MertX2/PowerStripHavoc/Firmware/firm/src/BQ2589x.cpp

/*                                                     https://oshwlab.com/ratti3
  _|_|_|                _|      _|      _|  _|_|_|     https://youtube.com/@Ratti3
  _|    _|    _|_|_|  _|_|_|_|_|_|_|_|            _|   https://projecthub.arduino.cc/Ratti3
  _|_|_|    _|    _|    _|      _|      _|    _|_|     https://ratti3.blogspot.com
  _|    _|  _|    _|    _|      _|      _|        _|   https://hackaday.io/Ratti3
  _|    _|    _|_|_|      _|_|    _|_|  _|  _|_|_|     https://www.hackster.io/Ratti3
                                                       https://github.com/Ratti3

Code forked from https://github.com/spencer1979/bq2589x

This file is part of https://github.com/Ratti3/BQ2589x-ATMEGA32U4-Charger-Powerbank-with-SSD1306-OLED

BQ2589x-ATMEGA32U4-Charger-Powerbank-with-SSD1306-OLED is free software: you can redistribute it and/or modify it under the terms of the
GNU General Public License as published by the Free Software Foundation, either version 3 of the License, or (at your option) any later version.
BQ2589x-ATMEGA32U4-Charger-Powerbank-with-SSD1306-OLED is distributed in the hope that it will be useful, but WITHOUT ANY WARRANTY;
without even the implied warranty of MERCHANTABILITY or FITNESS FOR A PARTICULAR PURPOSE. See the GNU General Public License for more details.
You should have received a copy of the GNU General Public License along with BQ2589x-ATMEGA32U4-Charger-Powerbank-with-SSD1306-OLED. If not, see <https://www.gnu.org/licenses/>.
*/

#include "BQ2589x.h"

int bq2589x::begin(TwoWire *theWire, uint8_t addr)
{
    _wire = theWire;
    _i2caddr = addr;
    return reset_chip();
}

int bq2589x::read_byte(uint8_t *data, uint8_t reg)
{

    int rtn;
    _wire->beginTransmission((uint8_t)_i2caddr);
    _wire->write(reg);
    rtn = _wire->endTransmission();

    _wire->requestFrom((uint8_t)_i2caddr, (uint8_t)1);
    delayMicroseconds(100);
    *data = _wire->read();

    if (rtn == I2C_OK)
    {
        return BQ2589X_OK; //TI lib uses 1 as failed
    }
    else
    {
        return BQ2589X_ERR; //TI lib uses 1 as failed
    }
}

int bq2589x::write_byte(uint8_t reg, uint8_t data)
{
    int rtn;
    _wire->beginTransmission((uint8_t)_i2caddr);
    _wire->write((uint8_t)reg);
    _wire->write((uint8_t)data);
    rtn = _wire->endTransmission();

    if (rtn == I2C_OK)
    {
        return BQ2589X_OK; //TI lib uses 1 as failed
    }
    else
    {
        return BQ2589X_ERR; //TI lib uses 1 as failed
    }
}

int bq2589x::update_bits(uint8_t reg, uint8_t mask, uint8_t data)
{
    int ret;
    uint8_t tmp;

    ret = read_byte(&tmp, reg);

    if (ret)
        return ret;

    tmp &= ~mask;
    tmp |= data & mask;

    return write_byte(reg, tmp);
}

int bq2589x::get_vbus_type()
{
    uint8_t val = 0;
    int ret;

    ret = read_byte(&val, BQ2589X_REG_0B);
    if (ret)
        return (BQ2589X_VBUS_UNKNOWN);
    val &= BQ2589X_VBUS_STAT_MASK;
    val >>= BQ2589X_VBUS_STAT_SHIFT;

    return val;
}

String bq2589x::get_vbus_type_text()
{
    switch (get_vbus_type()) {
    case 0:
        return BQ2589X_VBUS_STAT_00;
        break;
    case 1:
        return BQ2589X_VBUS_STAT_01;
        break;
    case 2:
        return BQ2589X_VBUS_STAT_02;
        break;
    case 3:
        return BQ2589X_VBUS_STAT_03;
        break;
    case 4:
        return BQ2589X_VBUS_STAT_04;
        break;
    case 5:
        return BQ2589X_VBUS_STAT_05;
        break;
    case 6:
        return BQ2589X_VBUS_STAT_06;
        break;
    case 7:
        return BQ2589X_VBUS_STAT_07;
        break;
    default:
        return BQ2589X_VBUS_STAT_XX;
        break;
    }
}

int bq2589x::enable_otg()
{
    uint8_t val = BQ2589X_OTG_ENABLE << BQ2589X_OTG_CONFIG_SHIFT;
    return update_bits(BQ2589X_REG_03, BQ2589X_OTG_CONFIG_MASK, val);
}

int bq2589x::disable_otg()
{
    uint8_t val = BQ2589X_OTG_DISABLE << BQ2589X_OTG_CONFIG_SHIFT;
    return update_bits(BQ2589X_REG_03, BQ2589X_OTG_CONFIG_MASK, val);
}

bool bq2589x::is_otg_enabled()
{
    uint8_t val;

    read_byte(&val, BQ2589X_REG_03);
    val &= BQ2589X_OTG_CONFIG_MASK;
    val >>= BQ2589X_OTG_CONFIG_SHIFT;

    return (bool)(val);
}

int bq2589x::set_otg_voltage(uint16_t volt)
{
    uint8_t val = 0;

    if (volt < BQ2589X_BOOSTV_BASE)
        volt = BQ2589X_BOOSTV_BASE;
    if (volt > BQ2589X_BOOSTV_BASE + (BQ2589X_BOOSTV_MASK >> BQ2589X_BOOSTV_SHIFT) * BQ2589X_BOOSTV_LSB)
        volt = BQ2589X_BOOSTV_BASE + (BQ2589X_BOOSTV_MASK >> BQ2589X_BOOSTV_SHIFT) * BQ2589X_BOOSTV_LSB;

    val = ((volt - BQ2589X_BOOSTV_BASE) / BQ2589X_BOOSTV_LSB) << BQ2589X_BOOSTV_SHIFT;
    return update_bits(BQ2589X_REG_0A, BQ2589X_BOOSTV_MASK, val);
}

int bq2589x::get_otg_voltage()
{
    uint8_t val;
    int volt;
    int ret;

    ret = read_byte(&val, BQ2589X_REG_0A);
    if (ret)
    {
        return ret;
    }
    else
    {
        volt = (BQ2589X_BOOSTV_BASE + ((val & BQ2589X_BOOSTV_MASK) >> BQ2589X_BOOSTV_SHIFT) * BQ2589X_BOOSTV_LSB);
        return volt;
    }
}

int bq2589x::set_otg_current(int curr)
{
    uint8_t temp;

    if (curr == 500)
        temp = BQ2589X_BOOST_LIM_500MA;
    else if (curr == 750)
        temp = BQ2589X_BOOST_LIM_750MA;
    else if (curr == 1200)
        temp = BQ2589X_BOOST_LIM_1200MA;
    else if (curr == 1400)
        temp = BQ2589X_BOOST_LIM_1400MA;
    else if (curr == 1650)
        temp = BQ2589X_BOOST_LIM_1650MA;
    else if (curr == 1875)
        temp = BQ2589X_BOOST_LIM_1875MA;
    else if (curr == 2150)
        temp = BQ2589X_BOOST_LIM_2150MA;
    else
        temp = BQ2589X_BOOST_LIM_1400MA;

    return update_bits(BQ2589X_REG_0A, BQ2589X_BOOST_LIM_MASK, temp << BQ2589X_BOOST_LIM_SHIFT);
}

int bq2589x::get_otg_current()
{
    uint8_t val;
    int curr;
    int ret;

    ret = read_byte(&val, BQ2589X_REG_0A);
    if (ret)
    {
        return ret;
    }
    else
    {
        curr = (val & BQ2589X_BOOST_LIM_MASK) >> BQ2589X_BOOST_LIM_SHIFT;
        if (curr == 0)
            ret = BQ2589X_BOOST_LIM_500MA_VALUE;
        else if (curr == 1)
            ret = BQ2589X_BOOST_LIM_750MA_VALUE;
        else if (curr == 2)
            ret = BQ2589X_BOOST_LIM_1200MA_VALUE;
        else if (curr == 3)
            ret = BQ2589X_BOOST_LIM_1400MA_VALUE;
        else if (curr == 4)
            ret = BQ2589X_BOOST_LIM_1650MA_VALUE;
        else if (curr == 5)
            ret = BQ2589X_BOOST_LIM_1875MA_VALUE;
        else if (curr == 6)
            ret = BQ2589X_BOOST_LIM_2150MA_VALUE;
    }
    return ret;
}

int bq2589x::enable_charger()
{
    uint8_t val = BQ2589X_CHG_ENABLE << BQ2589X_CHG_CONFIG_SHIFT;
    return update_bits(BQ2589X_REG_03, BQ2589X_CHG_CONFIG_MASK, val);
}

int bq2589x::disable_charger()
{
    uint8_t val = BQ2589X_CHG_DISABLE << BQ2589X_CHG_CONFIG_SHIFT;
    return update_bits(BQ2589X_REG_03, BQ2589X_CHG_CONFIG_MASK, val);
}

bool bq2589x::is_charge_enabled()
{
    uint8_t val;

    read_byte(&val, BQ2589X_REG_03);
    val &= BQ2589X_CHG_CONFIG_MASK;
    val >>= BQ2589X_CHG_CONFIG_SHIFT;

    return (bool)(val);
}

int bq2589x::enable_bat_loaden()
{
    uint8_t val = BQ2589X_BAT_LOADEN_ENABLE << BQ2589X_BAT_LOADEN_SHIFT;
    return update_bits(BQ2589X_REG_03, BQ2589X_BAT_LOADEN_MASK, val);
}

int bq2589x::disable_bat_loaden()
{
    uint8_t val = BQ2589X_BAT_LOADEN_DISABLE << BQ2589X_BAT_LOADEN_SHIFT;
    return update_bits(BQ2589X_REG_03, BQ2589X_BAT_LOADEN_MASK, val);
}

/* interfaces that can be called by other module */
int bq2589x::adc_start(bool oneshot)
{
    uint8_t val;
    int ret;

    ret = read_byte(&val, BQ2589X_REG_02);
    if (ret)
    {
        return ret;
    }

    if (((val & BQ2589X_CONV_RATE_MASK) >> BQ2589X_CONV_RATE_SHIFT) == BQ2589X_ADC_CONTINUE_ENABLE)
        return BQ2589X_OK; /*is doing continuous scan*/
    if (oneshot)
        ret = update_bits(BQ2589X_REG_02, BQ2589X_CONV_START_MASK, BQ2589X_CONV_START << BQ2589X_CONV_START_SHIFT);
    else
        ret = update_bits(BQ2589X_REG_02, BQ2589X_CONV_RATE_MASK, BQ2589X_ADC_CONTINUE_ENABLE << BQ2589X_CONV_RATE_SHIFT);
    return ret;
}

int bq2589x::adc_stop()
{
    return update_bits(BQ2589X_REG_02, BQ2589X_CONV_RATE_MASK, BQ2589X_ADC_CONTINUE_DISABLE << BQ2589X_CONV_RATE_SHIFT);
}

int bq2589x::adc_read_battery_volt()
{
    uint8_t val;
    int volt;
    int ret;
    ret = read_byte(&val, BQ2589X_REG_0E);

    if (ret)
    {
        return ret;
    }
    else
    {
        volt = (BQ2589X_BATV_BASE + ((val & BQ2589X_BATV_MASK) >> BQ2589X_BATV_SHIFT) * BQ2589X_BATV_LSB);
        return volt;
    }
}

int bq2589x::adc_read_sys_volt()
{
    uint8_t val;
    int volt;
    int ret;
    ret = read_byte(&val, BQ2589X_REG_0F);

    if (ret)
    {
        return ret;
    }
    else
    {
        volt = BQ2589X_SYSV_BASE + ((val & BQ2589X_SYSV_MASK) >> BQ2589X_SYSV_SHIFT) * BQ2589X_SYSV_LSB;
        return volt;
    }
}

int bq2589x::adc_read_vbus_volt()
{
    uint8_t val;
    int volt;
    int ret;
    ret = read_byte(&val, BQ2589X_REG_11);

    if (ret)
    {
        return ret;
    }
    else
    {
        volt = BQ2589X_VBUSV_BASE + ((val & BQ2589X_VBUSV_MASK) >> BQ2589X_VBUSV_SHIFT) * BQ2589X_VBUSV_LSB;
        return volt;
    }
}

int bq2589x::adc_read_temperature()
{
    uint8_t val;
    int temp;
    int ret;
    ret = read_byte(&val, BQ2589X_REG_10);

    if (ret)
    {
        return ret;
    }
    else
    {
        temp = BQ2589X_TSPCT_BASE + ((val & BQ2589X_TSPCT_MASK) >> BQ2589X_TSPCT_SHIFT) * BQ2589X_TSPCT_LSB;
        return temp;
    }
}

int bq2589x::adc_read_charge_current()
{
    uint8_t val;
    int volt;
    int ret;
    ret = read_byte(&val, BQ2589X_REG_12);

    if (ret)
    {
        return ret;
    }
    else
    {
        volt = (int)(BQ2589X_ICHGR_BASE + ((val & BQ2589X_ICHGR_MASK) >> BQ2589X_ICHGR_SHIFT) * BQ2589X_ICHGR_LSB);
        return volt;
    }
}

int bq2589x::set_charge_current(int curr)
{
    uint8_t ichg;
    ichg = (curr - BQ2589X_ICHG_BASE) / BQ2589X_ICHG_LSB;
    return update_bits(BQ2589X_REG_04, BQ2589X_ICHG_MASK, ichg << BQ2589X_ICHG_SHIFT);
}

int bq2589x::get_charge_current()
{
    uint8_t val;
    int current;
    int ret;

    ret = read_byte(&val, BQ2589X_REG_04);
    if (ret)
    {
        return ret;
    }
    else
    {
        current = (BQ2589X_ICHG_BASE + ((val & BQ2589X_ICHG_MASK) >> BQ2589X_ICHG_SHIFT) * BQ2589X_ICHG_LSB);
        return current;
    }
}

int bq2589x::set_term_current(int curr)
{
    uint8_t iterm;

    iterm = (curr - BQ2589X_ITERM_BASE) / BQ2589X_ITERM_LSB;
    return update_bits(BQ2589X_REG_05, BQ2589X_ITERM_MASK, iterm << BQ2589X_ITERM_SHIFT);
}

int bq2589x::set_prechg_current(int curr)
{
    uint8_t iprechg;

    iprechg = (curr - BQ2589X_IPRECHG_BASE) / BQ2589X_IPRECHG_LSB;
    return update_bits(BQ2589X_REG_05, BQ2589X_IPRECHG_MASK, iprechg << BQ2589X_IPRECHG_SHIFT);
}

int bq2589x::set_charge_voltage(int volt)
{
    uint8_t val;

    val = (volt - BQ2589X_VREG_BASE) / BQ2589X_VREG_LSB;
    return update_bits(BQ2589X_REG_06, BQ2589X_VREG_MASK, val << BQ2589X_VREG_SHIFT);
}

int bq2589x::get_charge_voltage()
{
    uint8_t val;
    int volt;
    int ret;

    ret = read_byte(&val, BQ2589X_REG_06);
    if (ret)
    {
        return ret;
    }
    else
    {
        volt = (BQ2589X_VREG_BASE + ((val & BQ2589X_VREG_MASK) >> BQ2589X_VREG_SHIFT) * BQ2589X_VREG_LSB);
        return volt;
    }
}

int bq2589x::set_input_volt_limit(int volt)
{
    uint8_t val;

    val = (volt - BQ2589X_VINDPM_BASE) / BQ2589X_VINDPM_LSB;
    return update_bits(BQ2589X_REG_0D, BQ2589X_VINDPM_MASK, val << BQ2589X_VINDPM_SHIFT);
}

int bq2589x::set_input_current_limit(int curr)
{
    uint8_t val;

    val = (curr - BQ2589X_IINLIM_BASE) / BQ2589X_IINLIM_LSB;
    return update_bits(BQ2589X_REG_00, BQ2589X_IINLIM_MASK, val << BQ2589X_IINLIM_SHIFT);
}

int bq2589x::set_vindpm_offset(int offset)
{
    uint8_t val;

    val = (offset - BQ2589X_VINDPMOS_BASE) / BQ2589X_VINDPMOS_LSB;
    return update_bits(BQ2589X_REG_01, BQ2589X_VINDPMOS_MASK, val << BQ2589X_VINDPMOS_SHIFT);
}

int bq2589x::get_charging_status()
{
    uint8_t val = 0;
    int ret;

    ret = read_byte(&val, BQ2589X_REG_0B);
    if (ret)
    {
        return 0x04; //Error
    }
    val &= BQ2589X_CHRG_STAT_MASK;
    val >>= BQ2589X_CHRG_STAT_SHIFT;

    return val;
}

String bq2589x::get_charging_status_text()
{
    switch (get_charging_status())
    {
    case 0:
        return BQ2589X_CHRG_STAT_00;
        break;
    case 1:
        return BQ2589X_CHRG_STAT_01;
        break;
    case 2:
        return BQ2589X_CHRG_STAT_02;
        break;
    case 3:
        return BQ2589X_CHRG_STAT_03;
        break;
    default:
        return BQ2589X_CHRG_STAT_XX;
        break;
    }
}

int bq2589x::get_fault_status(byte status)
{
    uint8_t val = 0;
    uint8_t temp1 = 255;
    uint8_t temp2 = 255;
    int ret;

    ret = read_byte(&val, BQ2589X_REG_0C);
    if (ret)
    {
        return 0x04; //Error
    }
    switch (status) {
    case 7:
        temp1 = BQ2589X_FAULT_WDT_MASK;
        temp2 = BQ2589X_FAULT_WDT_SHIFT;
        break;
    case 6:
        temp1 = BQ2589X_FAULT_BOOST_MASK;
        temp2 = BQ2589X_FAULT_BOOST_SHIFT;
        break;
    case 4:
        temp1 = BQ2589X_FAULT_CHRG_MASK;
        temp2 = BQ2589X_FAULT_CHRG_SHIFT;
        break;
    case 3:
        temp1 = BQ2589X_FAULT_BAT_MASK;
        temp2 = BQ2589X_FAULT_BAT_SHIFT;
        break;
    case 0:
        temp1 = BQ2589X_FAULT_NTC_MASK;
        temp2 = BQ2589X_FAULT_NTC_SHIFT;
        break;
    }
    val &= temp1;
    val >>= temp2;
    return val;
}

void bq2589x::bq2589x_set_otg(int enable)
{
    int ret;

    if (enable)
    {
        ret = enable_otg();
        if (ret)
        {
            return;
        }
    }
    else
    {
        ret = disable_otg();
    }
}

int bq2589x::set_watchdog_timer(uint8_t timeout)
{
    return update_bits(BQ2589X_REG_07, BQ2589X_WDT_MASK, (uint8_t)((timeout - BQ2589X_WDT_BASE) / BQ2589X_WDT_LSB) << BQ2589X_WDT_SHIFT);
}

int bq2589x::disable_watchdog_timer()
{
    uint8_t val = BQ2589X_WDT_DISABLE << BQ2589X_WDT_SHIFT;
    return update_bits(BQ2589X_REG_07, BQ2589X_WDT_MASK, val);
}

int bq2589x::reset_watchdog_timer()
{
    uint8_t val = BQ2589X_WDT_RESET << BQ2589X_WDT_RESET_SHIFT;
    return update_bits(BQ2589X_REG_03, BQ2589X_WDT_RESET_MASK, val);
}

int bq2589x::force_dpdm()
{
    int ret;
    uint8_t val = BQ2589X_FORCE_DPDM << BQ2589X_FORCE_DPDM_SHIFT;

    ret = update_bits(BQ2589X_REG_02, BQ2589X_FORCE_DPDM_MASK, val);
    if (ret)
        return ret;

    //msleep(20);/*TODO: how much time needed to finish dpdm detect?*/
    return BQ2589X_OK;
}

int bq2589x::reset_chip()
{
    int ret;

    uint8_t val = BQ2589X_RESET << BQ2589X_RESET_SHIFT;
    ret = update_bits(BQ2589X_REG_14, BQ2589X_RESET_MASK, val);

    return ret;
}

int bq2589x::enter_ship_mode()
{
    int ret;

    uint8_t val = BQ2589X_BATFET_OFF << BQ2589X_BATFET_DIS_SHIFT;
    ret = update_bits(BQ2589X_REG_09, BQ2589X_BATFET_DIS_MASK, val);

    return ret;
}

int bq2589x::enter_hiz_mode()
{
    uint8_t val = BQ2589X_HIZ_ENABLE << BQ2589X_ENHIZ_SHIFT;
    return update_bits(BQ2589X_REG_00, BQ2589X_ENHIZ_MASK, val);
}

int bq2589x::exit_hiz_mode()
{
    uint8_t val = BQ2589X_HIZ_DISABLE << BQ2589X_ENHIZ_SHIFT;
    return update_bits(BQ2589X_REG_00, BQ2589X_ENHIZ_MASK, val);
}

int bq2589x::get_hiz_mode(uint8_t *state)
{
    uint8_t val;
    int ret;

    ret = read_byte(&val, BQ2589X_REG_00);
    if (ret)
        return ret;
    *state = (val & BQ2589X_ENHIZ_MASK) >> BQ2589X_ENHIZ_SHIFT;

    return BQ2589X_OK;
}

int bq2589x::pumpx_enable(int enable)
{
    uint8_t val;
    int ret;

    if (enable)
        val = BQ2589X_PUMPX_ENABLE << BQ2589X_EN_PUMPX_SHIFT;
    else
        val = BQ2589X_PUMPX_DISABLE << BQ2589X_EN_PUMPX_SHIFT;

    ret = update_bits(BQ2589X_REG_04, BQ2589X_EN_PUMPX_MASK, val);

    return ret;
}

int bq2589x::pumpx_increase_volt()
{
    uint8_t val;
    int ret;

    val = BQ2589X_PUMPX_UP << BQ2589X_PUMPX_UP_SHIFT;
    ret = update_bits(BQ2589X_REG_09, BQ2589X_PUMPX_UP_MASK, val);

    return ret;
}

int bq2589x::pumpx_increase_volt_done()
{
    uint8_t val;
    int ret;

    ret = read_byte(&val, BQ2589X_REG_09);
    if (ret)
        return ret;

    if (val & BQ2589X_PUMPX_UP_MASK)
        return BQ2589X_ERR; /* not finished*/
    else
        return BQ2589X_OK; /* pumpx up finished*/
}

int bq2589x::pumpx_decrease_volt()
{
    uint8_t val;
    int ret;

    val = BQ2589X_PUMPX_DOWN << BQ2589X_PUMPX_DOWN_SHIFT;
    ret = update_bits(BQ2589X_REG_09, BQ2589X_PUMPX_DOWN_MASK, val);

    return ret;
}

int bq2589x::pumpx_decrease_volt_done()
{
    uint8_t val;
    int ret;

    ret = read_byte(&val, BQ2589X_REG_09);
    if (ret)
        return ret;

    if (val & BQ2589X_PUMPX_DOWN_MASK)
        return BQ2589X_ERR; /* not finished*/
    else
        return BQ2589X_OK; /* pumpx down finished*/
}

int bq2589x::force_ico()
{
    uint8_t val;
    int ret;

    val = BQ2589X_FORCE_ICO << BQ2589X_FORCE_ICO_SHIFT;
    ret = update_bits(BQ2589X_REG_09, BQ2589X_FORCE_ICO_MASK, val);

    return ret;
}

int bq2589x::check_force_ico_done()
{
    uint8_t val;
    int ret;

    ret = read_byte(&val, BQ2589X_REG_14);
    if (ret)
        return ret;

    if (val & BQ2589X_ICO_OPTIMIZED_MASK)
        return BQ2589X_ERR; /*finished*/
    else
        return BQ2589X_OK; /* in progress*/
}

int bq2589x::enable_term(bool enable)
{
    uint8_t val;
    int ret;

    if (enable)
        val = BQ2589X_TERM_ENABLE << BQ2589X_EN_TERM_SHIFT;
    else
        val = BQ2589X_TERM_DISABLE << BQ2589X_EN_TERM_SHIFT;

    ret = update_bits(BQ2589X_REG_07, BQ2589X_EN_TERM_MASK, val);

    return ret;
}

int bq2589x::enable_auto_dpdm(bool enable)
{
    uint8_t val;
    int ret;

    if (enable)
        val = BQ2589X_AUTO_DPDM_ENABLE << BQ2589X_AUTO_DPDM_EN_SHIFT;
    else
        val = BQ2589X_AUTO_DPDM_DISABLE << BQ2589X_AUTO_DPDM_EN_SHIFT;

    ret = update_bits(BQ2589X_REG_02, BQ2589X_AUTO_DPDM_EN_MASK, val);

    return ret;
}

int bq2589x::use_absolute_vindpm(bool enable)
{
    uint8_t val;
    int ret;

    if (enable)
        val = BQ2589X_FORCE_VINDPM_ENABLE << BQ2589X_FORCE_VINDPM_SHIFT;
    else
        val = BQ2589X_FORCE_VINDPM_DISABLE << BQ2589X_FORCE_VINDPM_SHIFT;

    ret = update_bits(BQ2589X_REG_0D, BQ2589X_FORCE_VINDPM_MASK, val);

    return ret;
}

int bq2589x::enable_ico(bool enable)
{
    uint8_t val;
    int ret;

    if (enable)
        val = BQ2589X_ICO_ENABLE << BQ2589X_ICOEN_SHIFT;
    else
        val = BQ2589X_ICO_DISABLE << BQ2589X_ICOEN_SHIFT;

    ret = update_bits(BQ2589X_REG_02, BQ2589X_ICOEN_MASK, val);

    return ret;
}

int bq2589x::read_idpm_limit()
{
    uint8_t val;
    int curr;
    int ret;

    ret = read_byte(&val, BQ2589X_REG_13);
    if (ret)
    {
        return ret;
    }
    else
    {
        curr = BQ2589X_IDPM_LIM_BASE + ((val & BQ2589X_IDPM_LIM_MASK) >> BQ2589X_IDPM_LIM_SHIFT) * BQ2589X_IDPM_LIM_LSB;
        return curr;
    }
}

bool bq2589x::is_charge_done()
{
    uint8_t val;

    read_byte(&val, BQ2589X_REG_0B);
    val &= BQ2589X_CHRG_STAT_MASK;
    val >>= BQ2589X_CHRG_STAT_SHIFT;

    return (bool)(val == BQ2589X_CHRG_STAT_CHGDONE);
}

int bq2589x::detect_device(bq2589x_part_no *part_no, int *revision)
{
    uint8_t data;
    if (read_byte(&data, BQ2589X_REG_14) == 0)
    {
        *part_no = (bq2589x_part_no)((data & BQ2589X_PN_MASK) >> BQ2589X_PN_SHIFT);
        *revision = (data & BQ2589X_DEV_REV_MASK) >> BQ2589X_DEV_REV_SHIFT;
        return BQ2589X_OK;
    }
    return BQ2589X_ERR;
}

int bq2589x::enable_max_charge(bool enable)
{
    uint8_t val;
    uint8_t val1;
    int ret;

    if (enable)
    {
        val = BQ2589X_HVDCP_ENABLE << BQ2589X_HVDCPEN_SHIFT;
        val1 = BQ2589X_MAXC_ENABLE << BQ2589X_MAXCEN_SHIFT;
    }
    else
    {
        val = BQ2589X_HVDCP_DISABLE << BQ2589X_HVDCPEN_SHIFT;
        val1 = BQ2589X_MAXC_DISABLE << BQ2589X_MAXCEN_SHIFT;
    }

    ret = update_bits(BQ2589X_REG_02, BQ2589X_HVDCPEN_MASK, val);
    ret = update_bits(BQ2589X_REG_02, BQ2589X_MAXCEN_MASK, val1);

    return ret;
}

int bq2589x::read_reg(byte reg)
{
    uint8_t val;

    read_byte(&val, reg);

    return val;
}
